StaCu/BrightestDungeon/src/Secret.h

/*
thanks for playing brightest dungeon goodby

THANKS FOR PLAYING BRIGHTEST DUNGEON GOODBY

- .... .- -. -.- ... 
..-. --- .-. 
.--. .-.. .- -.-- .. -. --. 
-... .-. .. --. .... - . ... - 
-.. ..- -. --. . --- -. 
--. --- --- -.. -... -.-- 
 */

const uint8_t Sound::secret_code[] PROGMEM = {
    0b01100000,
    0b00001000,
    0b01100100,
    0b10010001,
    0b10000000,
    0b10110000,
    0b01001001,
    0b01011000,
    0b01001011,
    0b00010100,
    0b10000100,
    0b00100001,
    0b10010001,
    0b01100000,
    0b10010010,
    0b01010010,
    0b11010000,
    0b00100001,
    0b00100000,
    0b10010100,
    0b10000000,
    0b00100110,
    0b00100000,
    0b00100110,
    0b11010000,
    0b10000001,
    0b10010010,
    0b01010010,
    0b00100101,
    0b01100100,
    0b10110101,
    0b00100101,
    0b01100101,
    0b01100100,
    0b00100100,
    0b00001001,
    0b00010110,
};
